moioonjake/midi2trigger/kicad/midi2trigger_v1.1.sch

## KiCad design kicad/midi2trigger_v1.1.sch (2020-05-04)

Schematic: midi2trigger_v1.1.sch

Parts:
A1: Arduino_Nano_v3.x; Arduino_Nano
D1: 1N4148; D_T-1_P2.54mm_Vertical_AnodeUp
D2, D3, D4, D5, D6, D7, D8, D9, D10, D11, D12, D13: LED; LED_D3.0mm
J1: OUT1; Jack_3.5mm_QingPu_WQP-PJ398SM_Vertical_CircularHoles
J2: MIDI IN; PinHeader_1x02_P2.54mm_Vertical
J3: EURORACK POWERCONNECTOR; PinHeader_2x05_P2.54mm_Vertical
J4: MIDI THRU; PinHeader_1x03_P2.54mm_Vertical
J5: OUT2; Jack_3.5mm_QingPu_WQP-PJ398SM_Vertical_CircularHoles
J6: OUT4; Jack_3.5mm_QingPu_WQP-PJ398SM_Vertical_CircularHoles
J7: OUT6; Jack_3.5mm_QingPu_WQP-PJ398SM_Vertical_CircularHoles
J8: OUT3; Jack_3.5mm_QingPu_WQP-PJ398SM_Vertical_CircularHoles
J9: OUT5; Jack_3.5mm_QingPu_WQP-PJ398SM_Vertical_CircularHoles
J10: OUT8; Jack_3.5mm_QingPu_WQP-PJ398SM_Vertical_CircularHoles
J11: OUT7; Jack_3.5mm_QingPu_WQP-PJ398SM_Vertical_CircularHoles
J12: OUT11; Jack_3.5mm_QingPu_WQP-PJ398SM_Vertical_CircularHoles
J13: OUT9; Jack_3.5mm_QingPu_WQP-PJ398SM_Vertical_CircularHoles
J14: OUT12; Jack_3.5mm_QingPu_WQP-PJ398SM_Vertical_CircularHoles
J15: OUT10; Jack_3.5mm_QingPu_WQP-PJ398SM_Vertical_CircularHoles
R1, R2, R3, R5: 220; R_Axial_DIN0204_L3.6mm_D1.6mm_P2.54mm_Vertical
R4: 4.7K; R_Axial_DIN0204_L3.6mm_D1.6mm_P2.54mm_Vertical
R6, R7, R8, R9, R10, R11, R12, R13, R14, R15, R16, R17: 1K; R_Axial_DIN0204_L3.6mm_D1.6mm_P2.54mm_Vertical
U1: 6N136; DIP-8_W7.62mm
U2: LM78L05; TO-92_Inline

Notes on the sheet:
MIDI IN
MIDI THRU
POWER SECTION
ARDUINO
OUTPUTS
NOTE! Incorrect, should be pin4 instead pin1
